Grindo666/Stair-LEDs-LOFT-/LED Strip.kicad_sch

## KiCad design LED Strip.kicad_sch (2025-08-25)

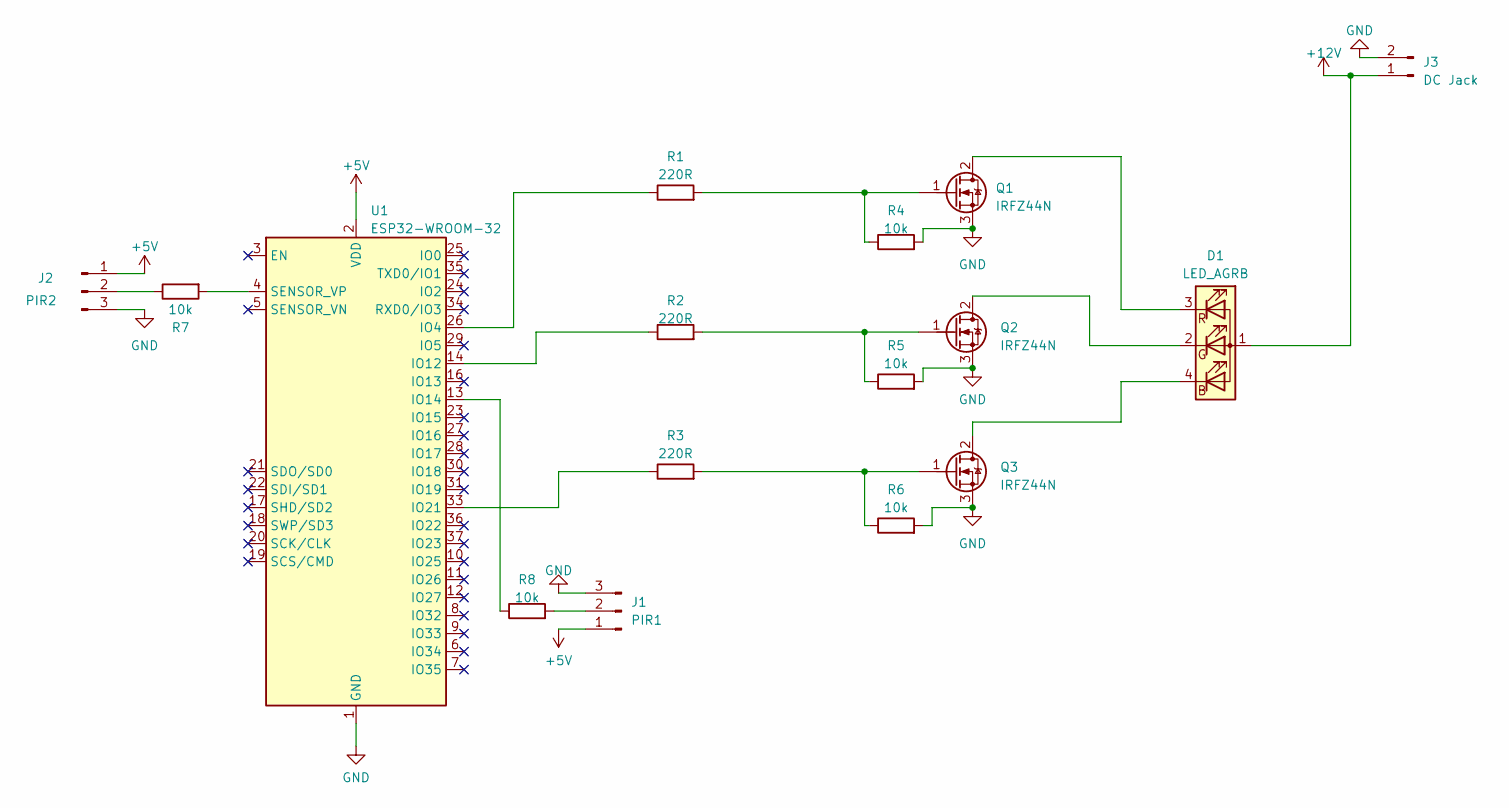
[picture p3: schematic LED Strip.kicad_sch]

Parts:
D1: LED_AGRB; SHDRRA2W64P0X254_1X4_508X1170X605P
J1: PIR1; Molex 3 way M RA header
J2: PIR2; Molex 3 way M RA header
J3: DC Jack; BarrelJack_CUI_PJ-063AH_Horizontal
Q1, Q2, Q3: IRFZ44N; TO-220-3_Vertical
R1, R2, R3: 220R; Resistor_L6.3mm_D2.5mm_P7.62mm_Horizontal
R4, R5, R6, R7, R8: 10k; Resistor_L6.3mm_D2.5mm_P7.62mm_Horizontal
U1: ESP32-WROOM-32; ESP32-C3-DevKitC-02

Connections:
+5V: J1.1, J2.1, U1.2 (VDD)
+12V: D1.1 (A), J3.1
GND: J1.3, J2.3, J3.2, Q1.3 (S), Q2.3 (S), Q3.3 (S), R4.2, R5.2, R6.2, U1.1 (GND), U1.15 (GND), U1.38 (GND), U1.39 (GND)
unnamed: D1.2 (GK), Q2.2 (D)
unnamed: D1.3 (RK), Q1.2 (D)
unnamed: D1.4 (BK), Q3.2 (D)
unnamed: J1.2, R8.2
unnamed: J2.2, R7.1
unnamed: Q1.1 (G), R1.2, R4.1
unnamed: Q2.1 (G), R2.2, R5.1
unnamed: Q3.1 (G), R3.2, R6.1
unnamed: R1.1, U1.26 (IO4)
unnamed: R2.1, U1.14 (IO12)
unnamed: R3.1, U1.33 (IO21)
unnamed: R7.2, U1.4 (SENSOR_VP)
unnamed: R8.1, U1.13 (IO14)
